augustoSantoni/LoomETec/Otros archivos/Diseños/Plegador/PAredPlegador1.stl

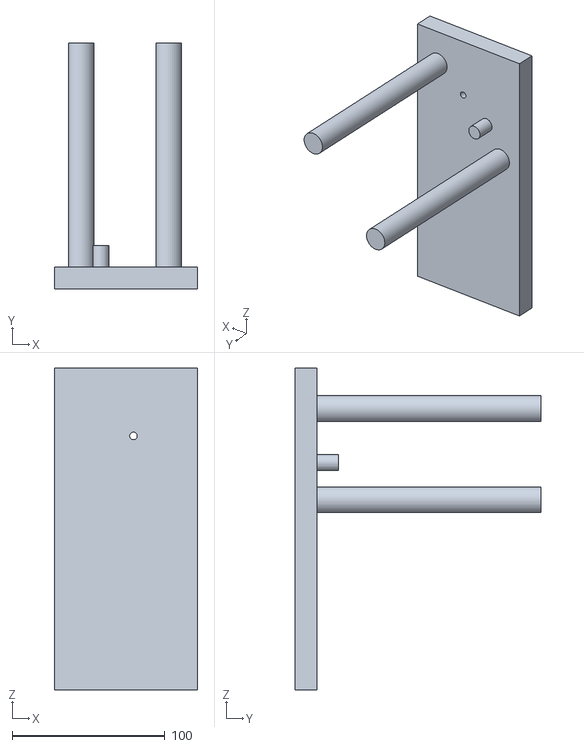
[picture p25: CAD file, 2026-07-26]
Otros archivos/Diseños/Plegador/PAredPlegador1.stl
93.8 x 161.5 x 211.2
