augustoSantoni/LoomETec/Archivos/LoomETec-Jacquard/Diseños/Calador/Caladror1.stl

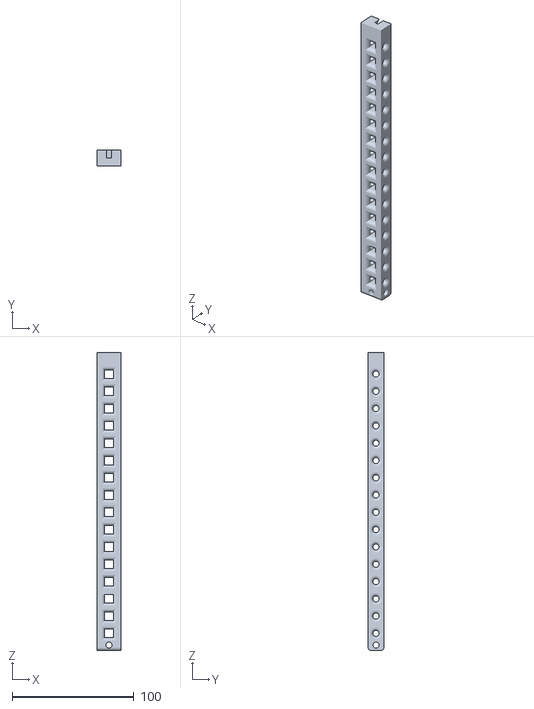
[picture p26: CAD file, 2026-07-26]
Archivos/LoomETec-Jacquard/Diseños/Calador/Caladror1.stl
19.8 x 13.2 x 245.2
