augustoSantoni/LoomETec/Archivos/LoomETec-Jacquard/Diseños/GuiaEjeX1.stl

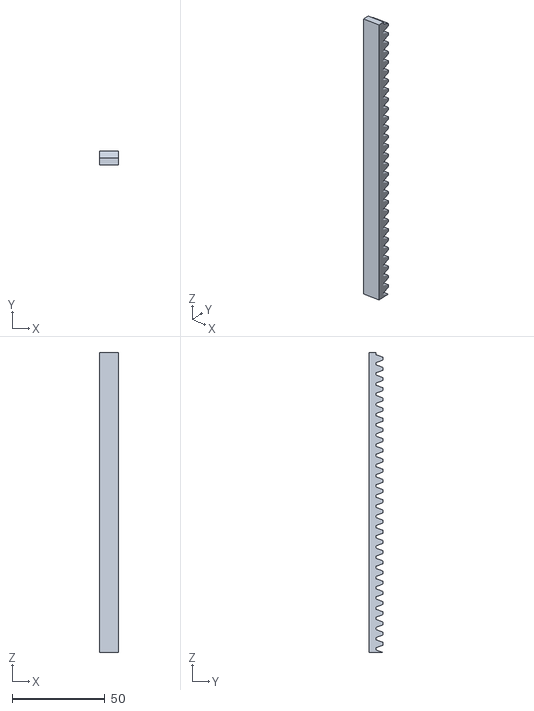
[picture p27: CAD file, 2026-07-30]
Archivos/LoomETec-Jacquard/Diseños/GuiaEjeX1.stl
10.0 x 7.75 x 162.0
