augustoSantoni/LoomETec/Archivos/LoomETec-Jacquard/Diseños/Lanza/Lanza3.stl

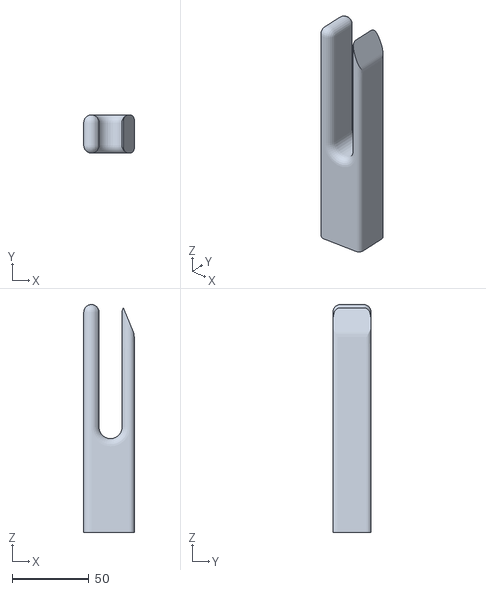
[picture p28: CAD file, 2026-07-26]
Archivos/LoomETec-Jacquard/Diseños/Lanza/Lanza3.stl
33.0 x 25.0 x 148.8
