augustoSantoni/LoomETec/Archivos/LoomETec-Jacquard/Diseños/Plegador-SoporteHilo/ConectorCaño-Mot.stl

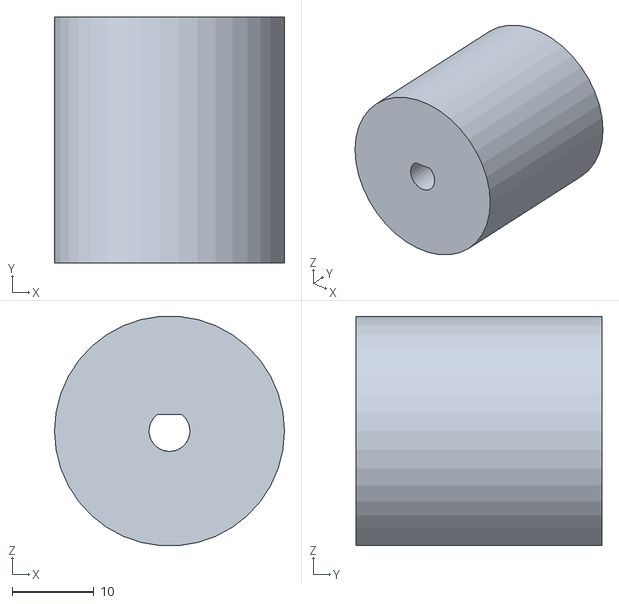
[picture p29: CAD file, 2026-07-26]
Archivos/LoomETec-Jacquard/Diseños/Plegador-SoporteHilo/ConectorCaño-Mot.stl
28.1 x 30.0 x 28.0
