augustoSantoni/LoomETec/Otros archivos/Diseños/Calador/Calador1.stl

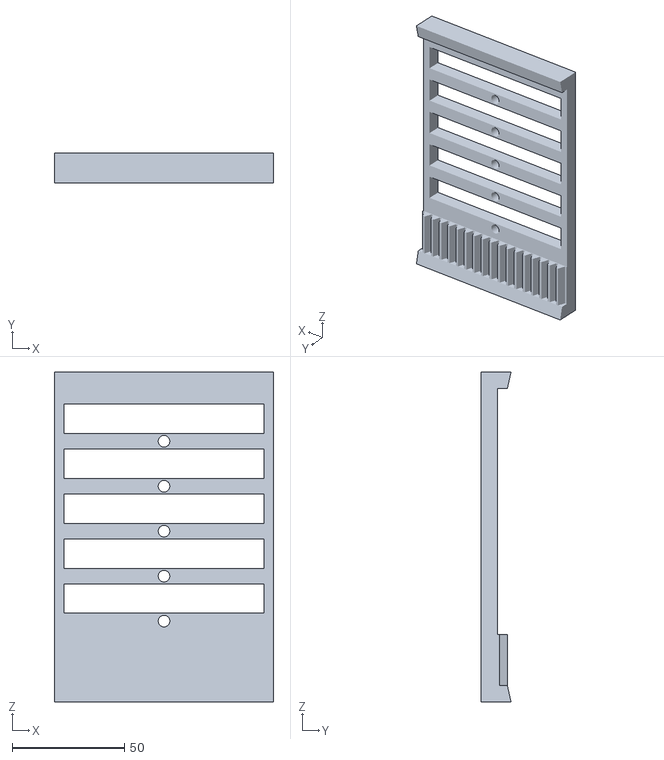
[picture p30: CAD file, 2026-07-26]
Otros archivos/Diseños/Calador/Calador1.stl
97.5 x 13.4 x 146.8
