augustoSantoni/LoomETec/Otros archivos/Diseños/Lanzadera/SoporteHiloLanza1.stl

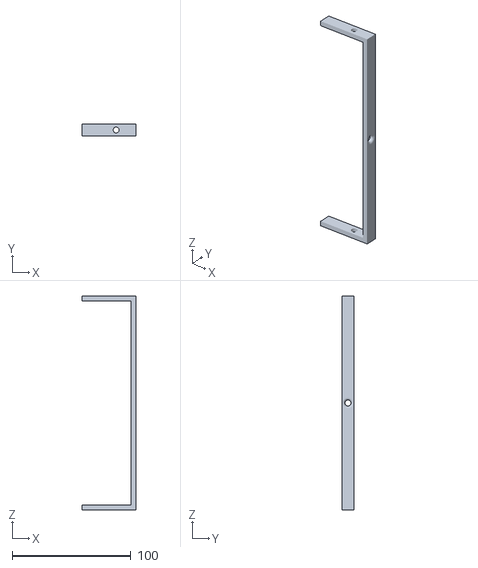
[picture p31: CAD file, 2026-07-26]
Otros archivos/Diseños/Lanzadera/SoporteHiloLanza1.stl
45.0 x 10.0 x 180.0
