augustoSantoni/LoomETec/Otros archivos/Diseños/Peine/TornilloPeine.stl

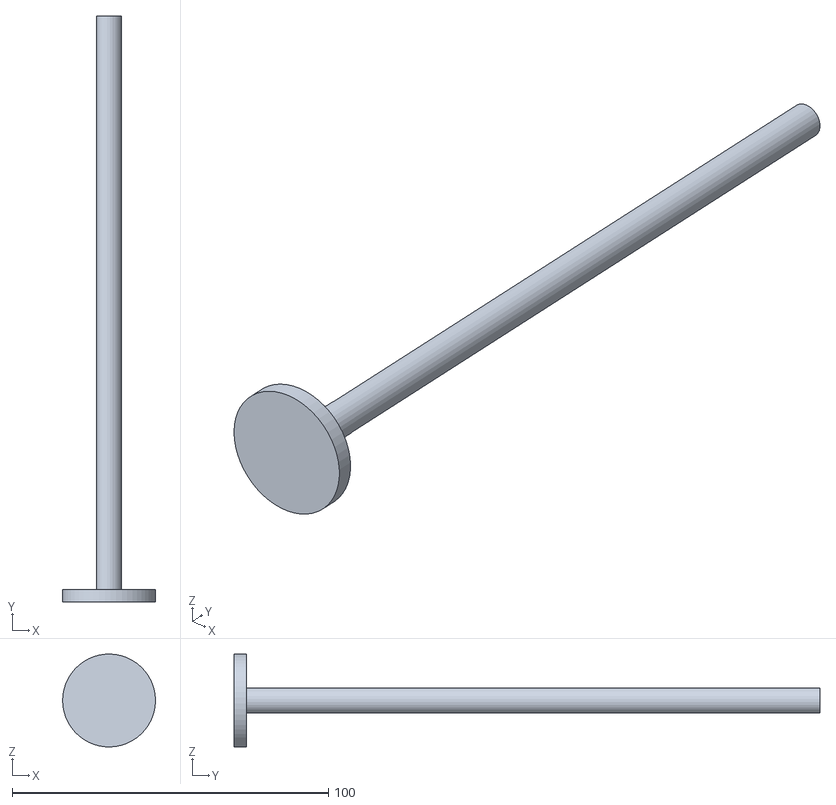
[picture p32: CAD file, 2026-07-26]
Otros archivos/Diseños/Peine/TornilloPeine.stl
29.4 x 185.4 x 29.4
