augustoSantoni/LoomETec/Otros archivos/Diseños/Plegador/Plegador1.stl

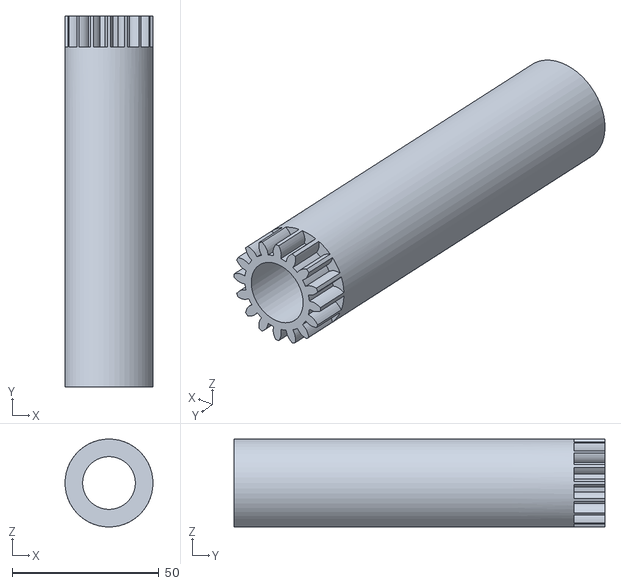
[picture p33: CAD file, 2026-07-26]
Otros archivos/Diseños/Plegador/Plegador1.stl
30.0 x 126.5 x 30.0
