augustoSantoni/LoomETec/Archivos/LoomETec-Jacquard/Diseños/Calador/EngranajeMovEjeX.stl

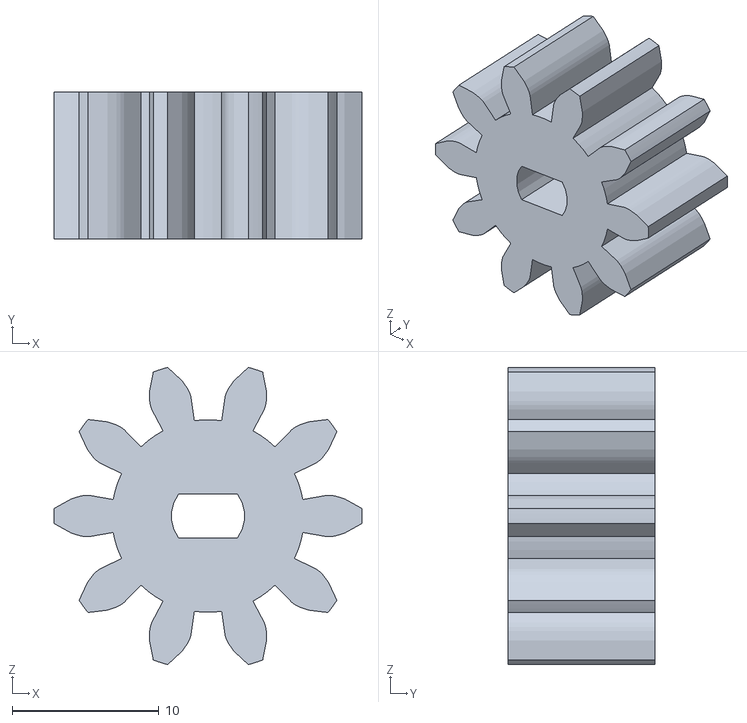
[picture p34: CAD file, 2026-07-26]
Archivos/LoomETec-Jacquard/Diseños/Calador/EngranajeMovEjeX.stl
21.0 x 10.0 x 20.3
