augustoSantoni/LoomETec/Otros archivos/Diseños/Calador/EngranajeCal.stl

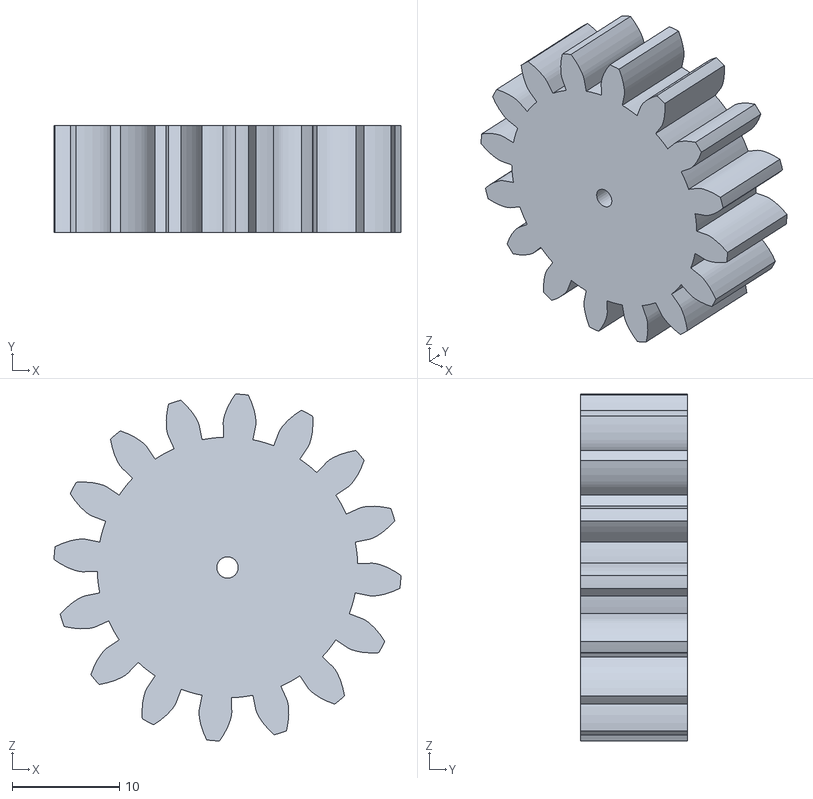
[picture p35: CAD file, 2026-07-26]
Otros archivos/Diseños/Calador/EngranajeCal.stl
32.4 x 10.0 x 32.4
