augustoSantoni/LoomETec/Otros archivos/Diseños/Lanzadera/SoporteHiloLanza2.stl

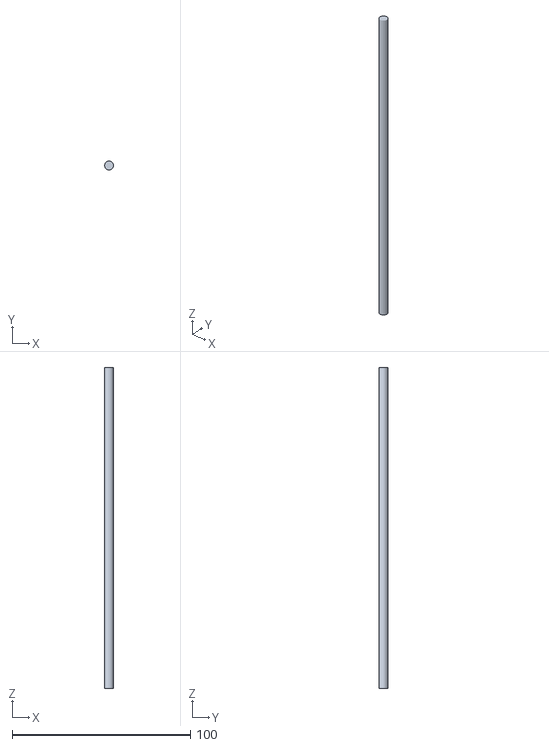
[picture p36: CAD file, 2026-07-26]
Otros archivos/Diseños/Lanzadera/SoporteHiloLanza2.stl
4.98 x 4.99 x 180.0
