augustoSantoni/LoomETec/Otros archivos/Diseños/Peine/ParedPeine1.stl

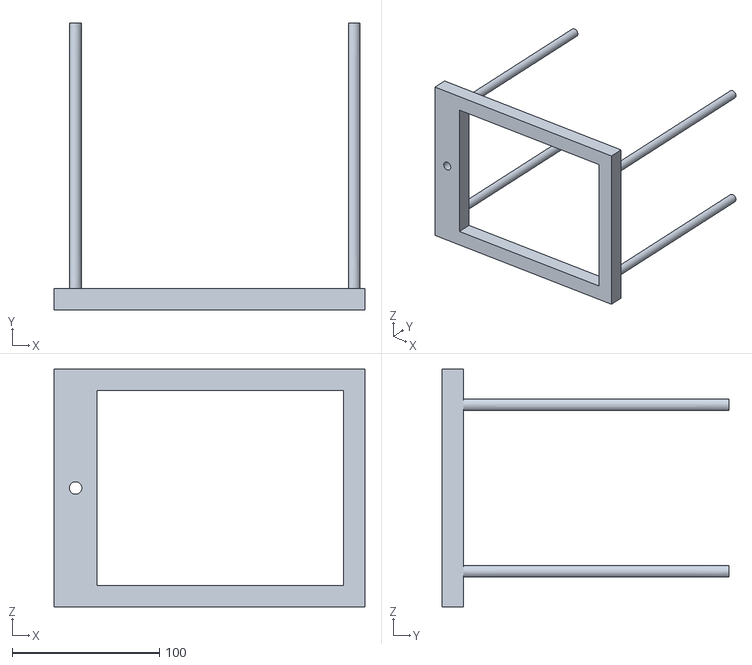
[picture p37: CAD file, 2026-07-26]
Otros archivos/Diseños/Peine/ParedPeine1.stl
211.2 x 195.0 x 161.5
