augustoSantoni/LoomETec/Otros archivos/Diseños/Plegador/EngranajePlegador.stl

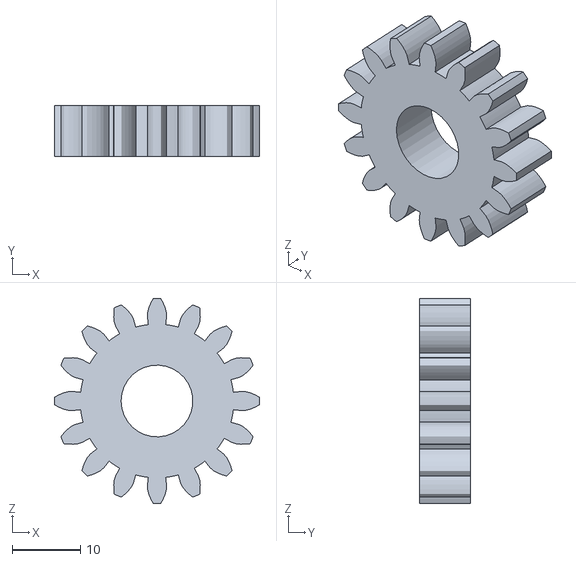
[picture p38: CAD file, 2026-07-26]
Otros archivos/Diseños/Plegador/EngranajePlegador.stl
30.0 x 7.50 x 30.0
