augustoSantoni/LoomETec/Archivos/LoomETec-Jacquard/Diseños/Calador/GuiaEjeX2.stl

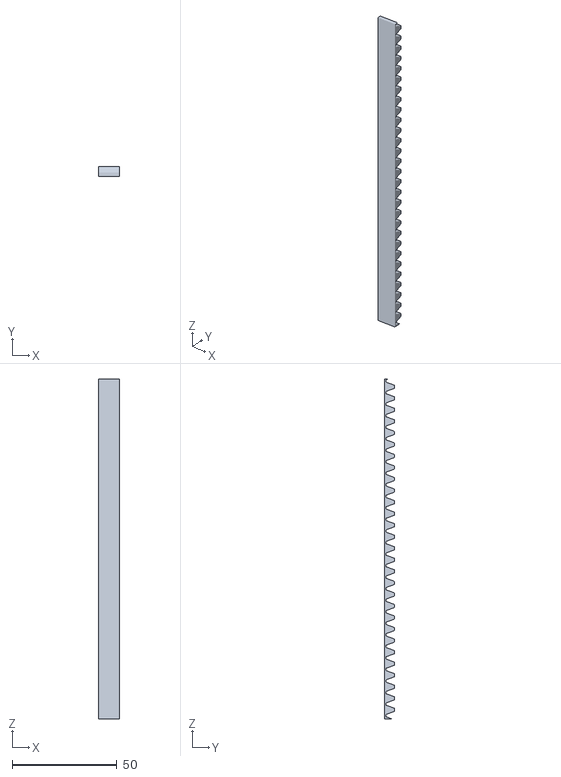
[picture p39: CAD file, 2026-07-26]
Archivos/LoomETec-Jacquard/Diseños/Calador/GuiaEjeX2.stl
10.0 x 4.75 x 162.0
