augustoSantoni/LoomETec/Archivos/LoomETec-Jacquard/Diseños/EngranajeActuadorEjeZ.stl

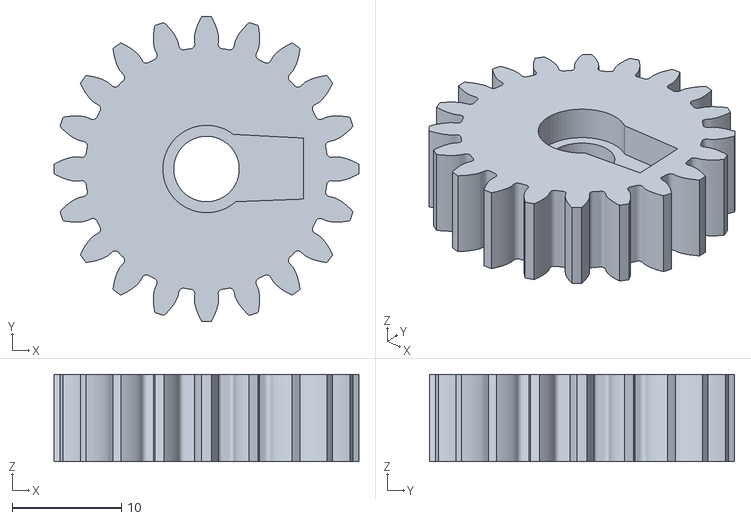
[picture p40: CAD file, 2026-07-30]
Archivos/LoomETec-Jacquard/Diseños/EngranajeActuadorEjeZ.stl
27.9 x 27.9 x 8.00
