augustoSantoni/LoomETec/Archivos/LoomETec-Jacquard/Diseños/Lanza/Receptor-Lanza.stl

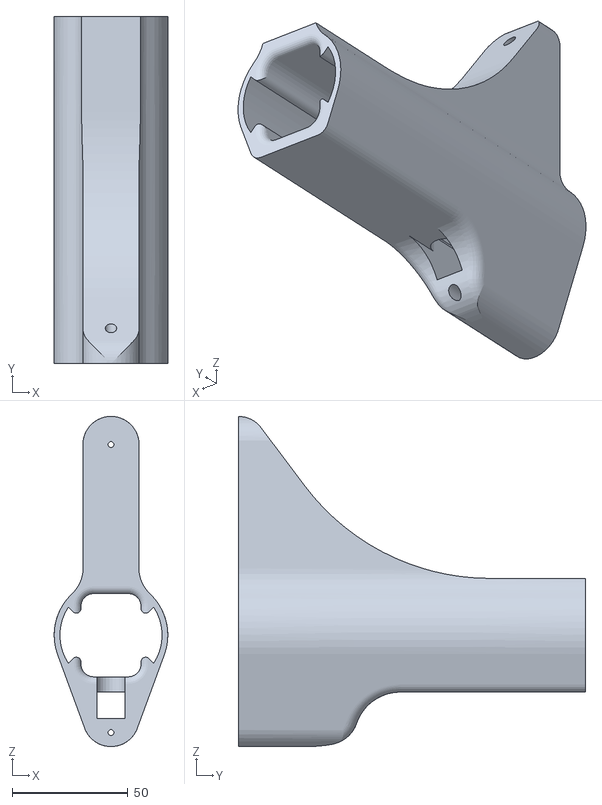
[picture p41: CAD file, 2026-07-26]
Archivos/LoomETec-Jacquard/Diseños/Lanza/Receptor-Lanza.stl
49.2 x 150.0 x 142.7
