augustoSantoni/LoomETec/Otros archivos/Diseños/Lanzadera/Lanzadera.stl

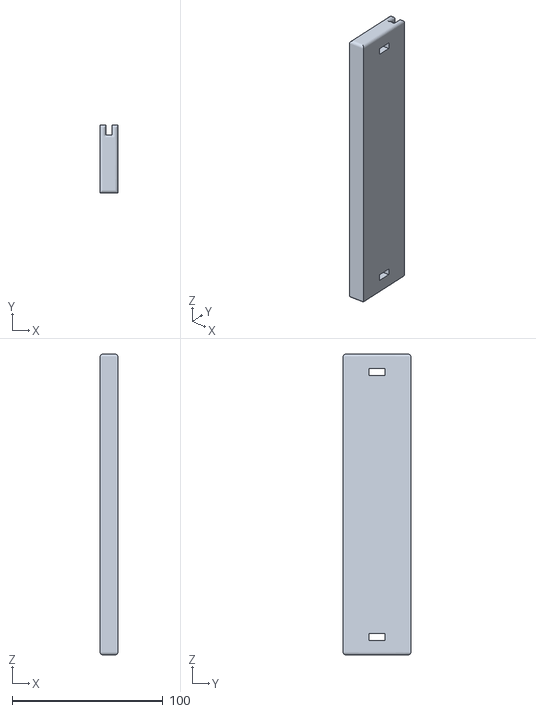
[picture p42: CAD file, 2026-07-26]
Otros archivos/Diseños/Lanzadera/Lanzadera.stl
12.0 x 45.0 x 200.0
