augustoSantoni/LoomETec/Otros archivos/Diseños/Peine/ParedPeine2.stl

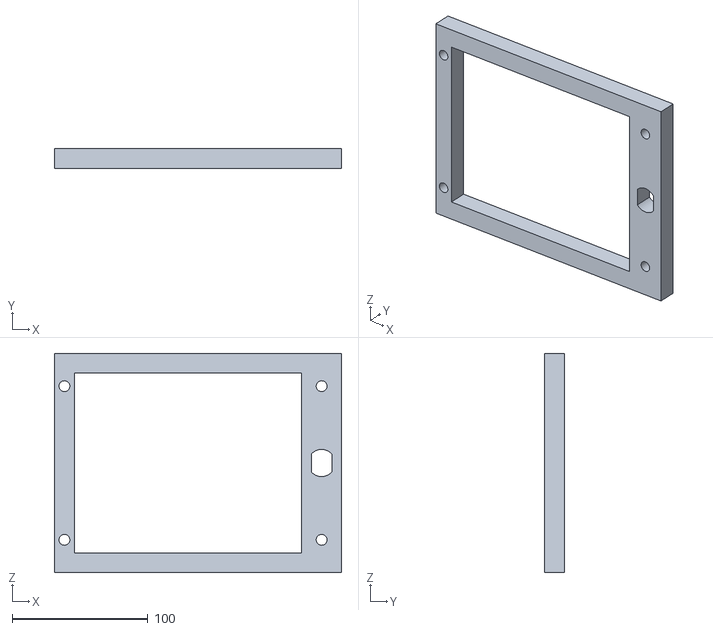
[picture p43: CAD file, 2026-07-26]
Otros archivos/Diseños/Peine/ParedPeine2.stl
211.2 x 14.6 x 161.5
