augustoSantoni/LoomETec/Archivos/LoomETec-Jacquard/Diseños/Calador/SoporteMot.stl

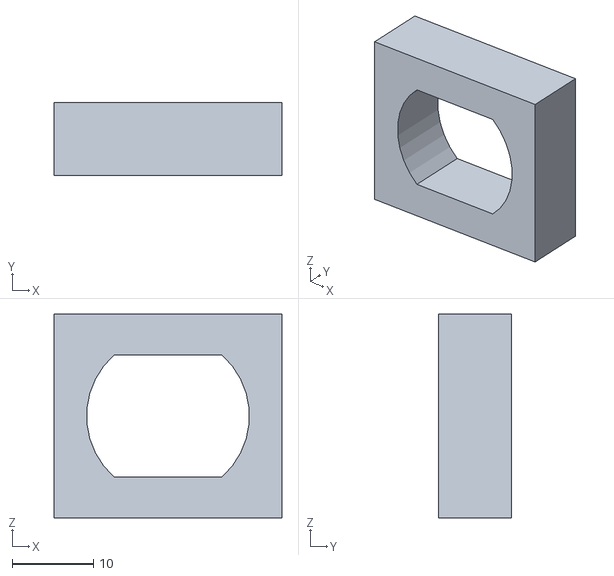
[picture p44: CAD file, 2026-07-26]
Archivos/LoomETec-Jacquard/Diseños/Calador/SoporteMot.stl
28.0 x 9.00 x 25.0
