augustoSantoni/LoomETec/Archivos/LoomETec-Jacquard/Diseños/Lanza/Lanza2.stl

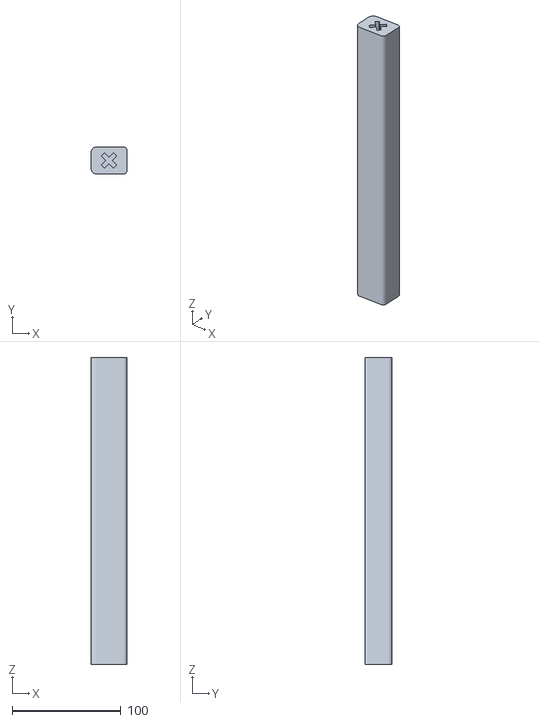
[picture p45: CAD file, 2026-07-26]
Archivos/LoomETec-Jacquard/Diseños/Lanza/Lanza2.stl
33.0 x 25.0 x 282.8
