augustoSantoni/LoomETec/Otros archivos/Diseños/Lanzadera/SoporteLanza1.stl

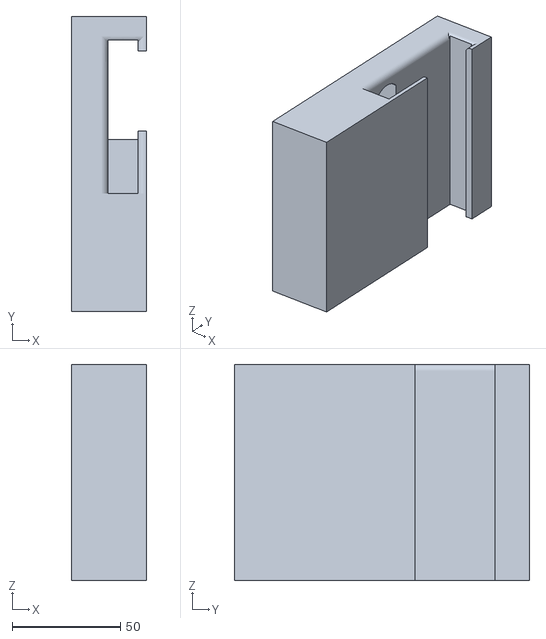
[picture p47: CAD file, 2026-07-26]
Otros archivos/Diseños/Lanzadera/SoporteLanza1.stl
34.9 x 136.6 x 100.0
