augustoSantoni/LoomETec/Otros archivos/Diseños/Plegador/PAredPlegador2.stl

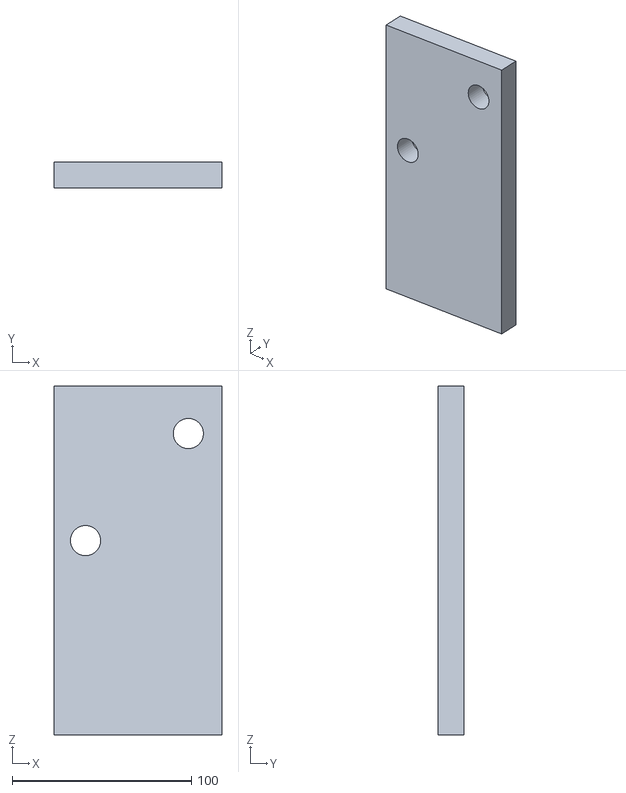
[picture p48: CAD file, 2026-07-26]
Otros archivos/Diseños/Plegador/PAredPlegador2.stl
93.8 x 14.6 x 194.9
