augustoSantoni/LoomETec/Archivos/LoomETec-Jacquard/Diseños/Calador/Calador2.stl

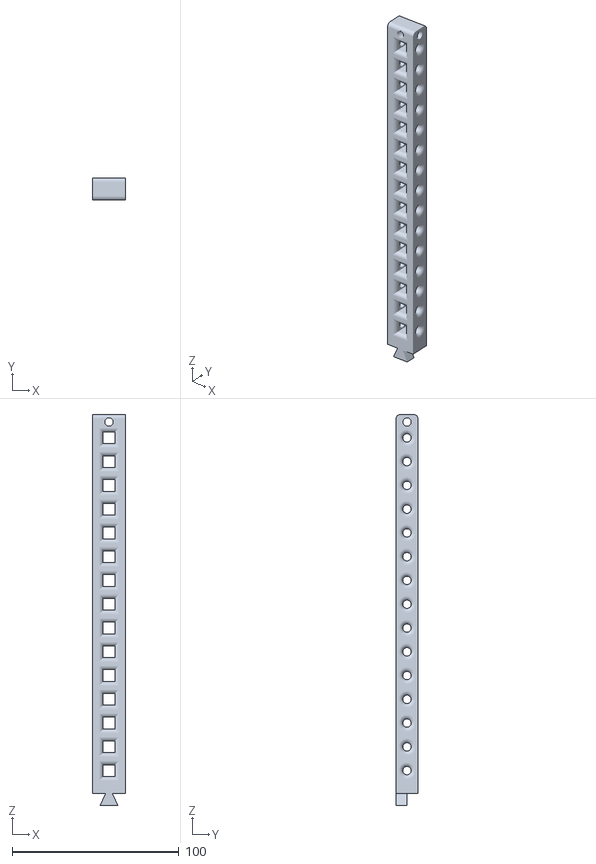
[picture p49: CAD file, 2026-07-26]
Archivos/LoomETec-Jacquard/Diseños/Calador/Calador2.stl
19.8 x 13.2 x 234.1
