augustoSantoni/LoomETec/Archivos/PCB/LIBRERIAS /Archivos 3d/uln2003a.step

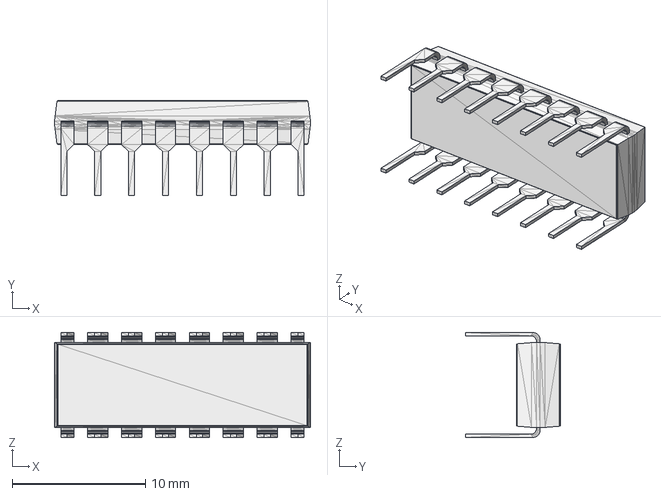
[picture p50: CAD file, 2026-07-26]
Archivos/PCB/LIBRERIAS /Archivos 3d/uln2003a.step
19.2 x 7.10 x 7.87 mm
