augustoSantoni/LoomETec/Archivos/LoomETec-Jacquard/Diseños/Calador/Base2.stl

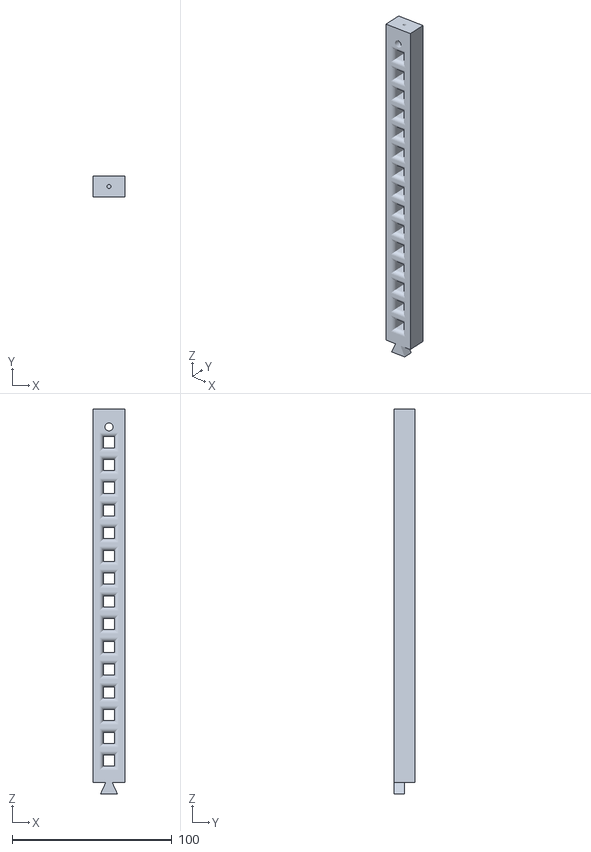
[picture p51: CAD file, 2026-07-26]
Archivos/LoomETec-Jacquard/Diseños/Calador/Base2.stl
19.8 x 13.2 x 240.9
