augustoSantoni/LoomETec/Archivos/LoomETec-Jacquard/Diseños/Calador/Paso2Engranaje-Cadena.stl

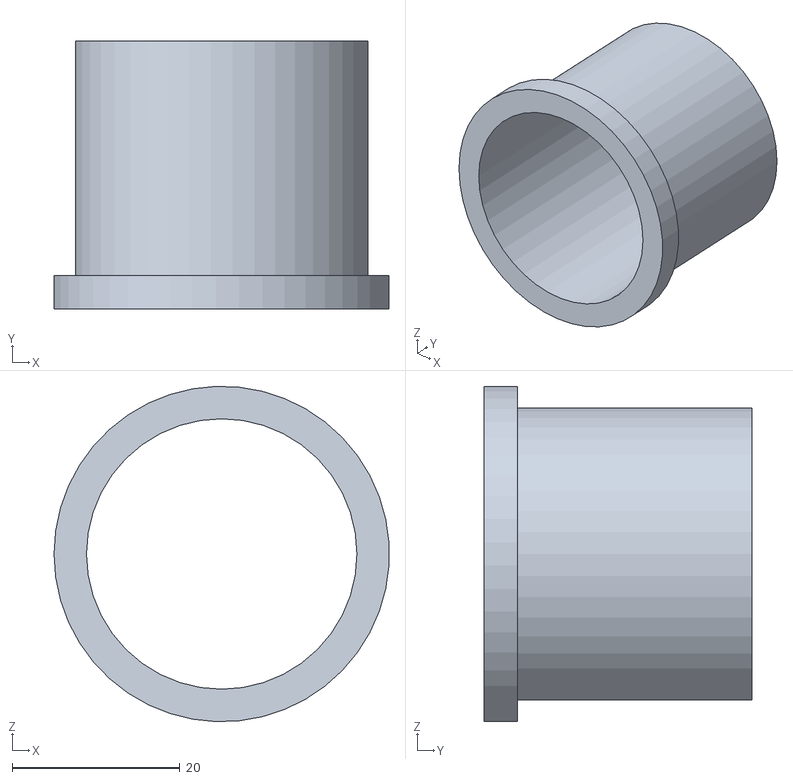
[picture p52: CAD file, 2026-07-26]
Archivos/LoomETec-Jacquard/Diseños/Calador/Paso2Engranaje-Cadena.stl
40.0 x 32.0 x 40.0
