augustoSantoni/LoomETec/Archivos/LoomETec-Jacquard/Diseños/Calador/ChasisActuadorEjeZ.stl

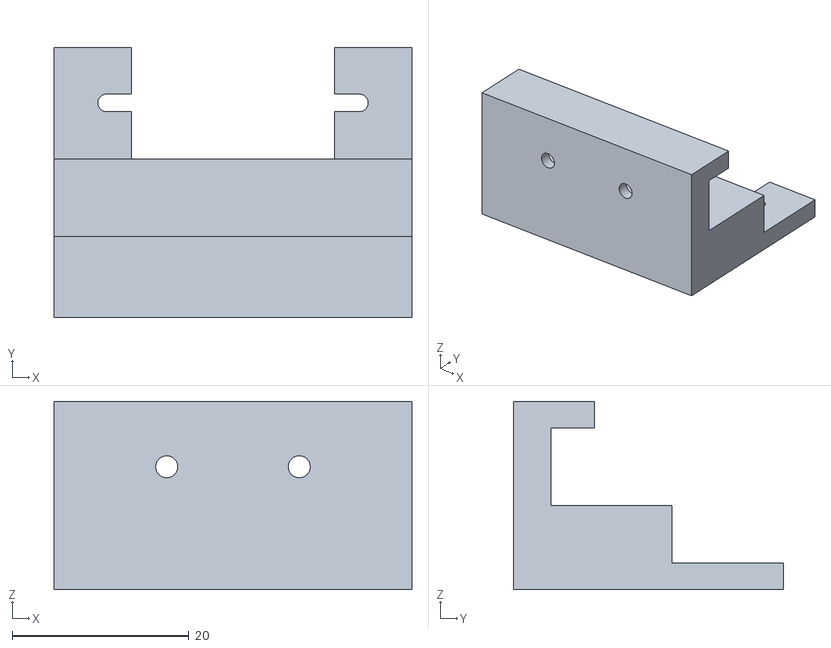
[picture p53: CAD file, 2026-07-26]
Archivos/LoomETec-Jacquard/Diseños/Calador/ChasisActuadorEjeZ.stl
40.5 x 30.5 x 21.3
