augustoSantoni/LoomETec/Archivos/LoomETec-Jacquard/Diseños/Calador/Pasador.stl

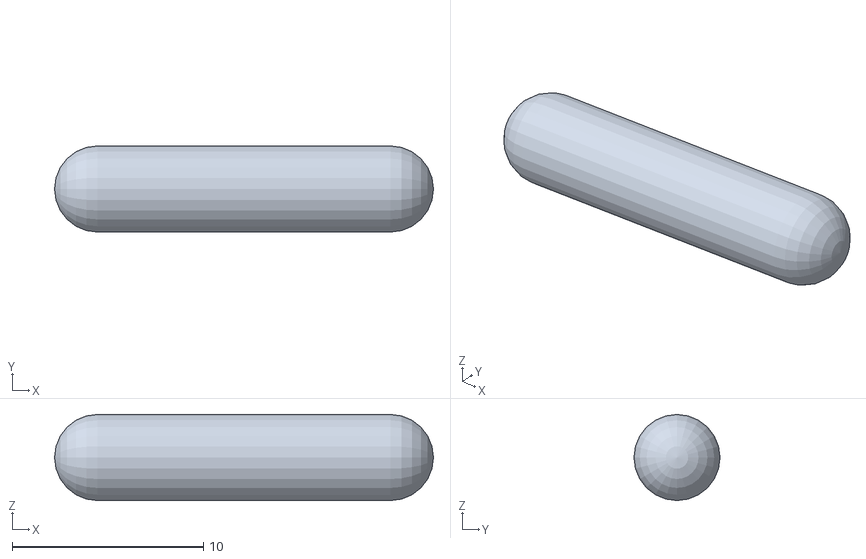
[picture p54: CAD file, 2026-07-26]
Archivos/LoomETec-Jacquard/Diseños/Calador/Pasador.stl
19.8 x 4.50 x 4.50
