augustoSantoni/LoomETec/Archivos/LoomETec-Jacquard/Diseños/Calador/Paso1Egranaje-Cadena.stl

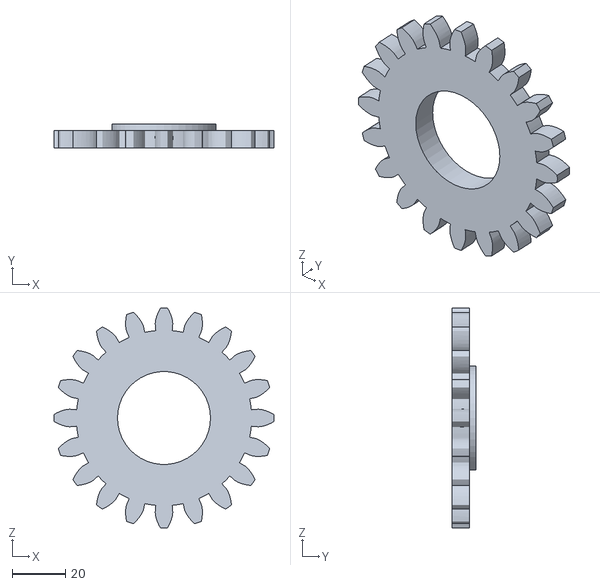
[picture p55: CAD file, 2026-07-26]
Archivos/LoomETec-Jacquard/Diseños/Calador/Paso1Egranaje-Cadena.stl
82.6 x 9.00 x 82.6
