augustoSantoni/LoomETec/Archivos/LoomETec-Jacquard/Diseños/Calador/Sujetador.stl

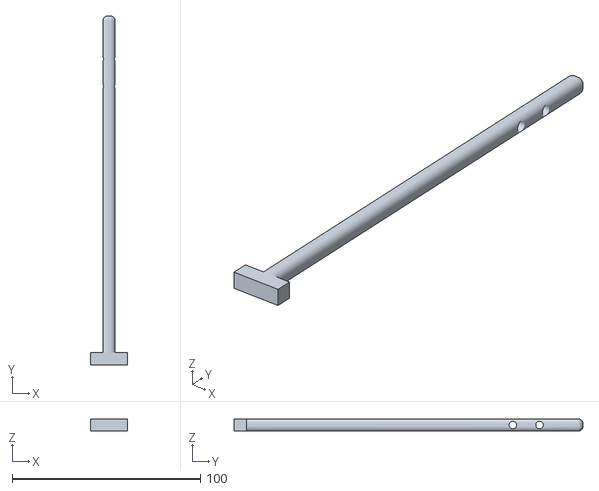
[picture p56: CAD file, 2026-07-26]
Archivos/LoomETec-Jacquard/Diseños/Calador/Sujetador.stl
19.8 x 185.6 x 6.60
