augustoSantoni/LoomETec/Archivos/LoomETec-Jacquard/Diseños/Calador/EngranajeMot.stl

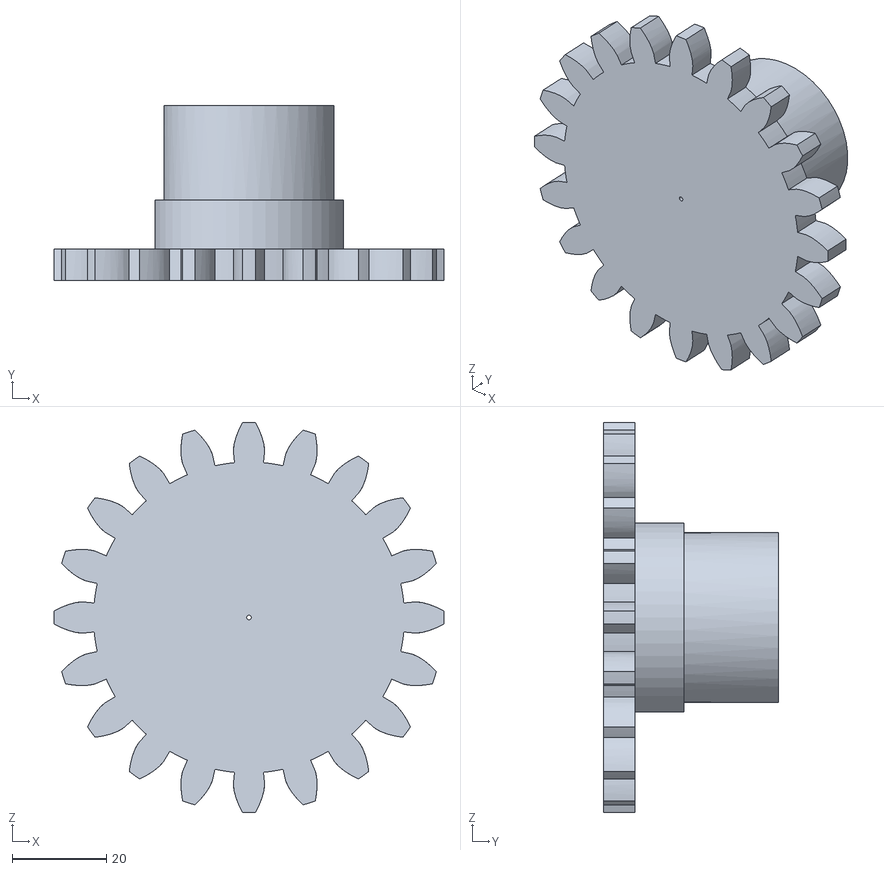
[picture p57: CAD file, 2026-07-26]
Archivos/LoomETec-Jacquard/Diseños/Calador/EngranajeMot.stl
82.6 x 37.0 x 82.6
