augustoSantoni/LoomETec/Archivos/LoomETec-Jacquard/Diseños/Calador/ActuadorEjeZ.stl

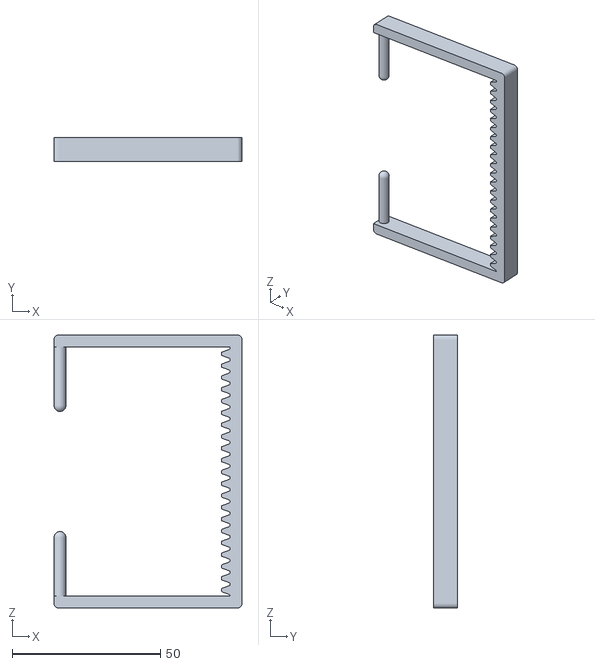
[picture p58: CAD file, 2026-07-26]
Archivos/LoomETec-Jacquard/Diseños/Calador/ActuadorEjeZ.stl
63.5 x 8.00 x 92.2
