augustoSantoni/LoomETec/Archivos/LoomETec-Jacquard/Diseños/Calador/TapaEngranajes.stl

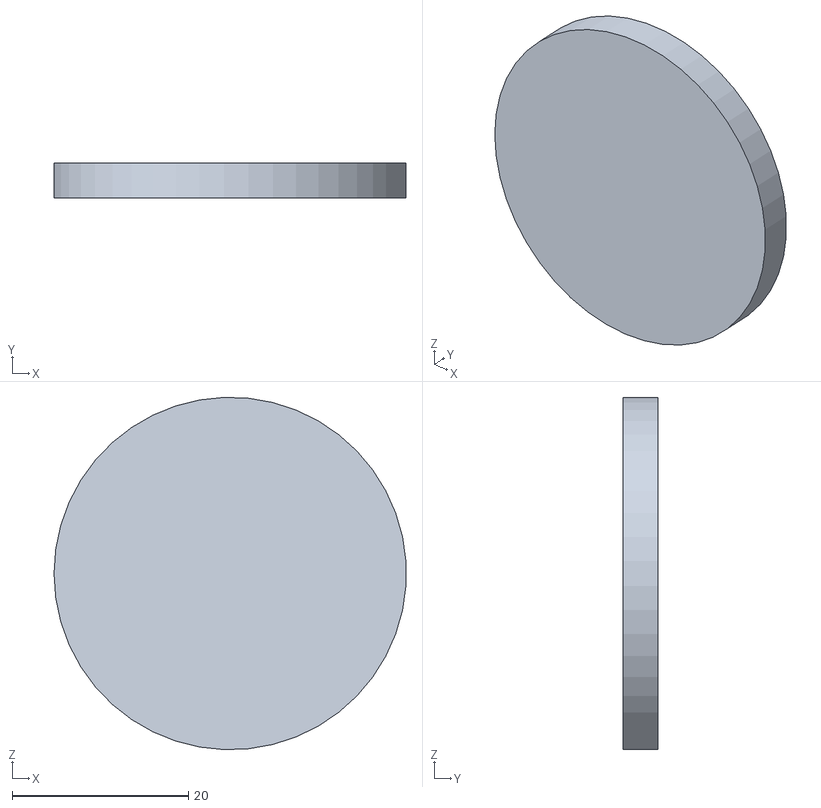
[picture p59: CAD file, 2026-07-26]
Archivos/LoomETec-Jacquard/Diseños/Calador/TapaEngranajes.stl
40.0 x 4.00 x 40.0
